accso/learning-iot/firmware/learningiot/html/pin-list-small.jpg

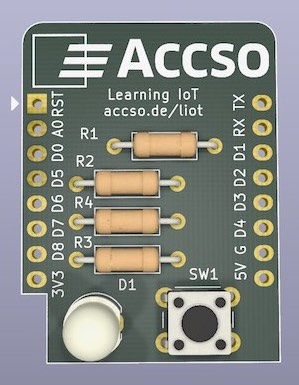
firmware/learningiot/html/pin-list-small.jpg
