accso/learning-iot/firmware/learningiot/html/pin-list-small.png

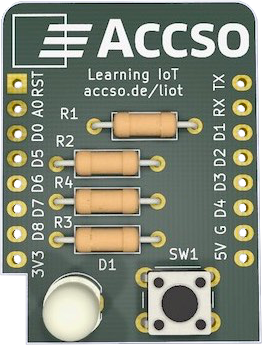
firmware/learningiot/html/pin-list-small.png
