accso/learning-iot/images/in-action.jpg

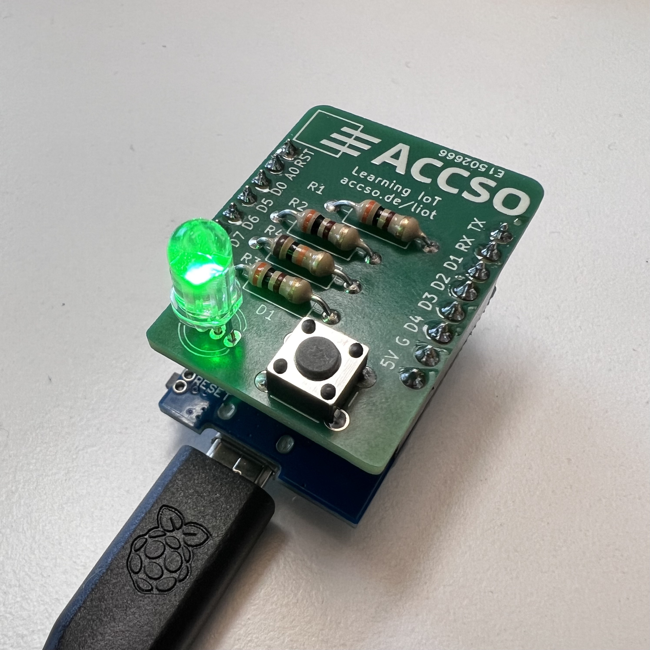
images/in-action.jpg
