accso/learning-iot/images/learning-iot.png

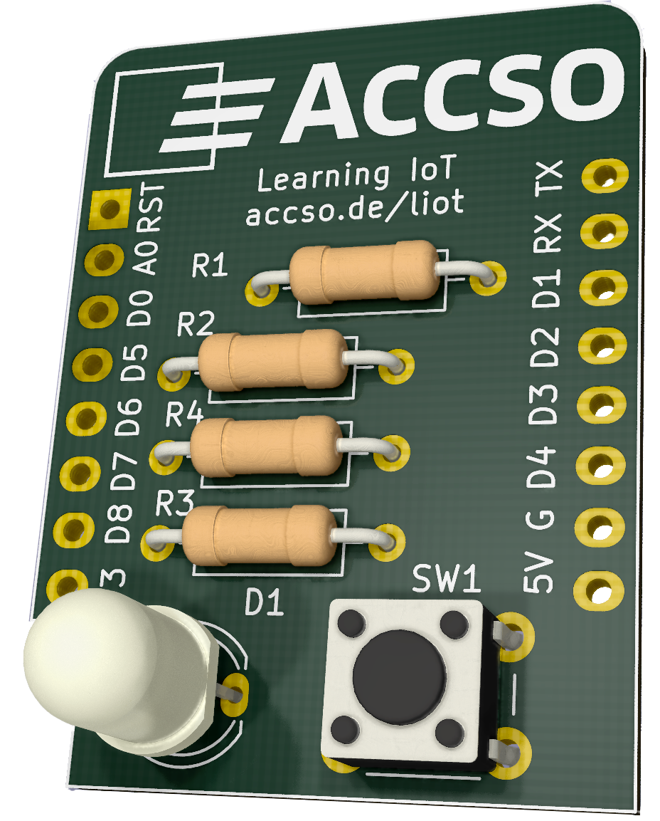
images/learning-iot.png
