accso/learning-iot/firmware/learningiot/appconfig.h

/*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
 *******************************************************************************
 */

/**
 *******************************************************************************
 **\file appconfig.c
 **
 ** App Configuration
 ** A detailed description is available at
 ** @link AppConfigGroup file description @endlink
 **
 ** History:
 ** - 2021-2-3  1.00  Manuel Schreiner
 *******************************************************************************
 */

#if !defined(__APPCONFIG_H__)
#define __APPCONFIG_H__

/* C binding of definitions if building with C++ compiler */
//#ifdef __cplusplus
//extern "C"
//{
//#endif

/**
 *******************************************************************************
 ** \defgroup AppConfigGroup App Configuration
 **
 ** Provided functions of AppConfig:
 **
 **
 *******************************************************************************
 */

//@{

/**
 *******************************************************************************
** \page appconfig_module_includes Required includes in main application
** \brief Following includes are required
** @code
** #include "appconfig.h"
** @endcode
**
 *******************************************************************************
 */

/**
 *******************************************************************************
 ** (Global) Include files
 *******************************************************************************
 */

#include "stdint.h"
#include "webconfig.h"

/**
 *******************************************************************************
 ** Global pre-processor symbols/macros ('#define') 
 *******************************************************************************
 */

#define APP_VERSION "V1.0.0"
#define APP_NAME "learning-iot"

#define INITIAL_SSID_STATION_MODE "MyWifi"
#define INITIAL_PASSORD_STATION_MODE "MyPassword"

#define INITIAL_WWW_NAME "admin"
#define INITIAL_WWW_PASS "admin"


/**
 *******************************************************************************
 ** Global type definitions ('typedef') 
 *******************************************************************************
 */

typedef struct __attribute__((__packed__)) stc_appconfig
{
  char ssidStation[32];
  char passwordStation[32];
  char wwwUser[32];
  char wwwPass[32];
  

  int32_t u32magic;
} stc_appconfig_t;

/**
 *******************************************************************************
 ** Global variable declarations ('extern', definition in C source)
 *******************************************************************************
 */

/**
 *******************************************************************************
 ** Global function prototypes ('extern', definition in C source) 
 *******************************************************************************
 */

#if defined(ARDUINO_ARCH_ESP8266)
void AppConfig_Init(ESP8266WebServer* pWebServerHandle);
#else
void AppConfig_Init(WebServer* pWebServerHandle);
#endif
void AppConfig_Write(void);
char* AppConfig_GetStaSsid(void);
char* AppConfig_GetStaPassword(void);
void AppConfig_SetStaSsid(char* ssid);
void AppConfig_SetStaPassword(char* pass);
char* AppConfig_GetWwwUser(void);
void AppConfig_SetWwwUser(char* WwwUser);
char* AppConfig_GetWwwPass(void);
void AppConfig_SetWwwPass(char* WwwPass);



//@} // AppConfigGroup

//#ifdef __cplusplus
//}
//#endif

#endif /* __APPCONFIG_H__ */

/**
 *******************************************************************************
 ** EOF (not truncated)
 *******************************************************************************
 */
